CedarGroveStudios/AD9833_FeatherWing/photos/DSC05793a lores.jpg

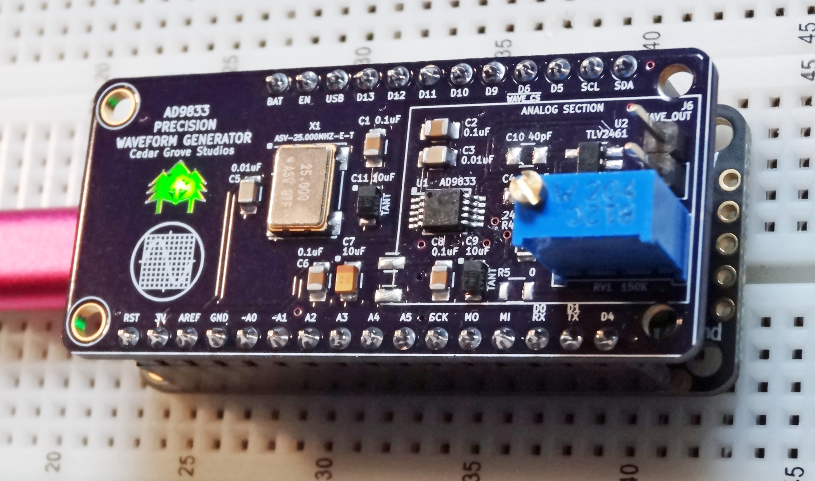
photos/DSC05793a lores.jpg
