CedarGroveStudios/AD9833_FeatherWing/photos/smooth ADSR algorithm.png

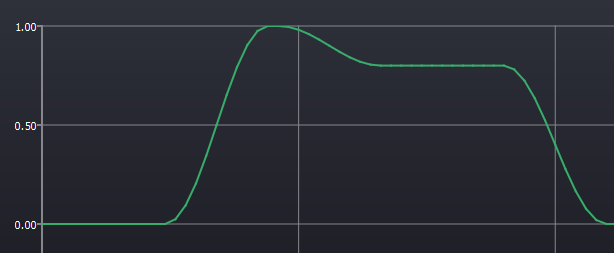
photos/smooth ADSR algorithm.png
