CedarGroveStudios/AD9833_FeatherWing/photos/waveform gen UI.jpg

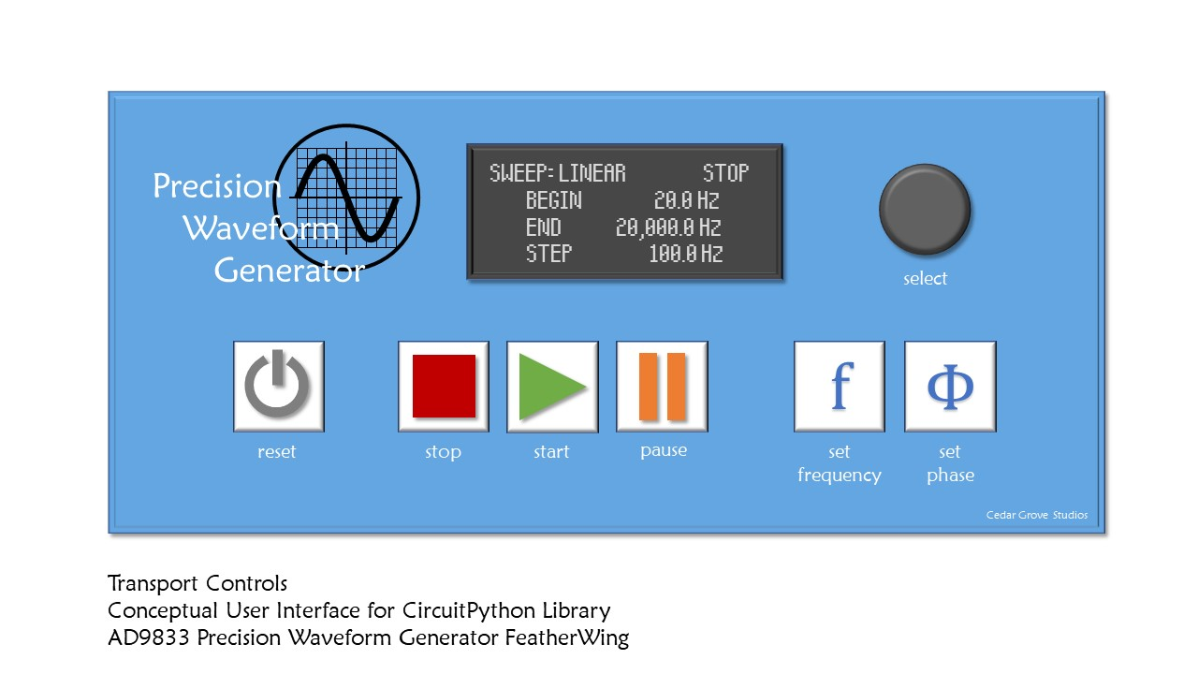
photos/waveform gen UI.jpg
