CedarGroveStudios/AD9833_FeatherWing/photos/Waveform_Generator closeup.png

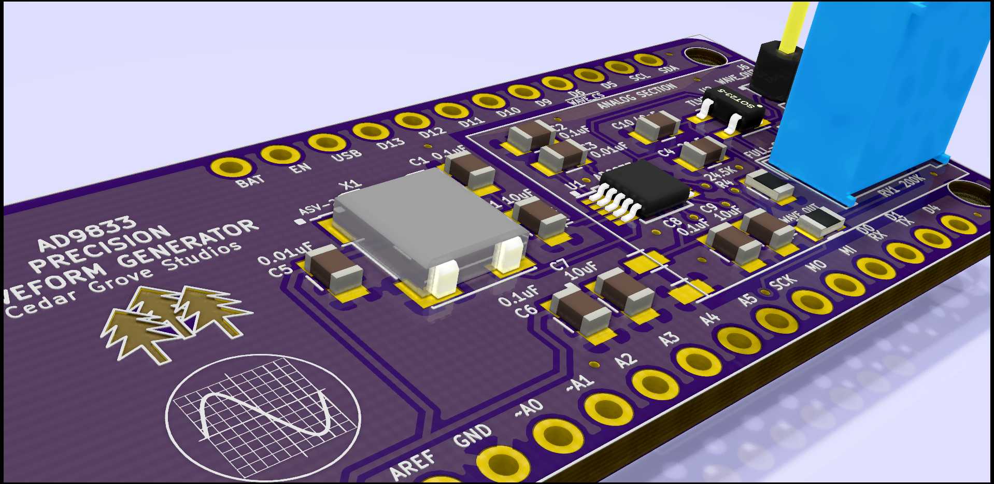
photos/Waveform_Generator closeup.png
