CedarGroveStudios/AD9833_FeatherWing/photos/Waveform_Generator edge.png

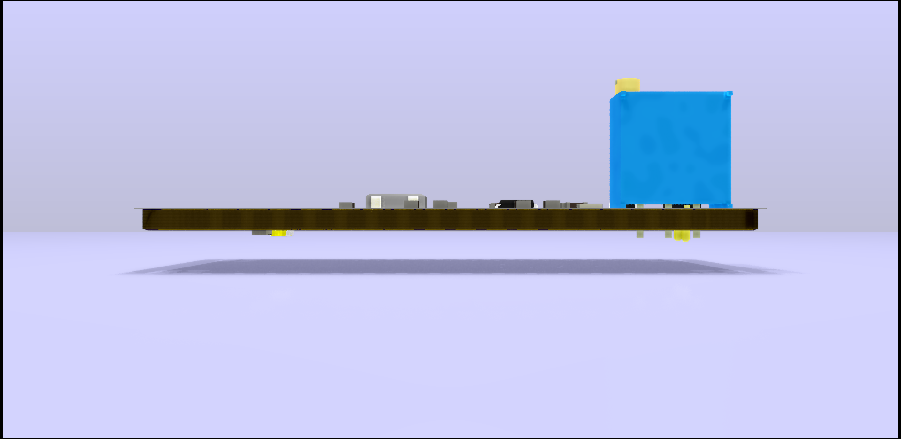
photos/Waveform_Generator edge.png
