CedarGroveStudios/AD9833_FeatherWing/photos/Waveform_Generator for fritzing act_size.png

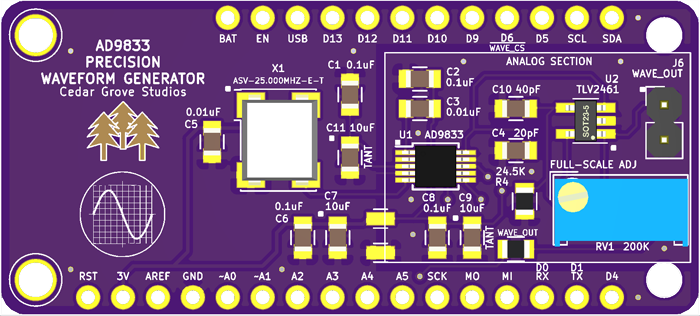
photos/Waveform_Generator for fritzing act_size.png
