CedarGroveStudios/AD9833_FeatherWing/photos/Waveform_Generator.png

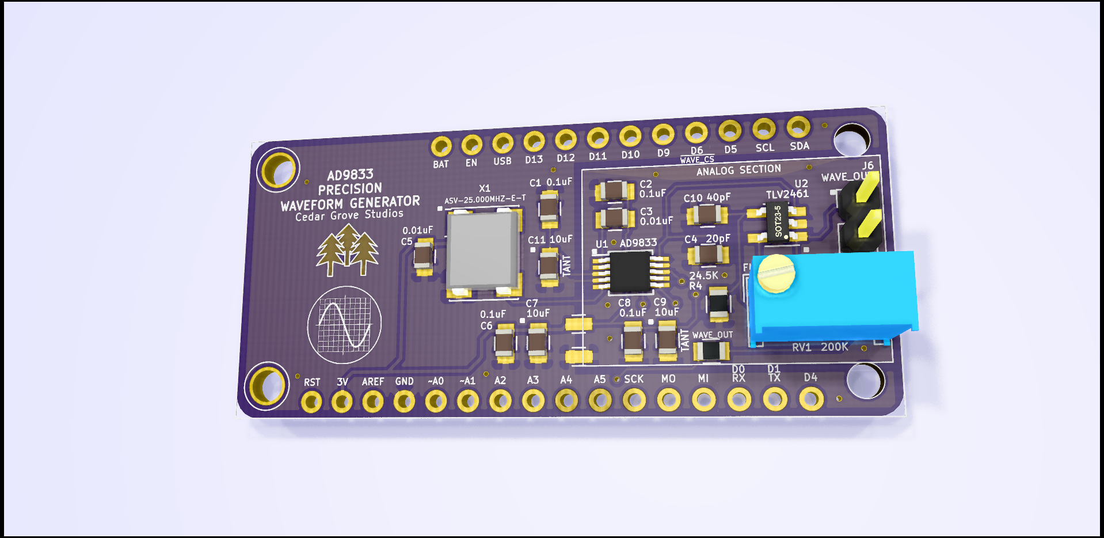
photos/Waveform_Generator.png
